kiu/nakabo/nakabo-avr64da32/nakabo-avr64da32-render-B.png

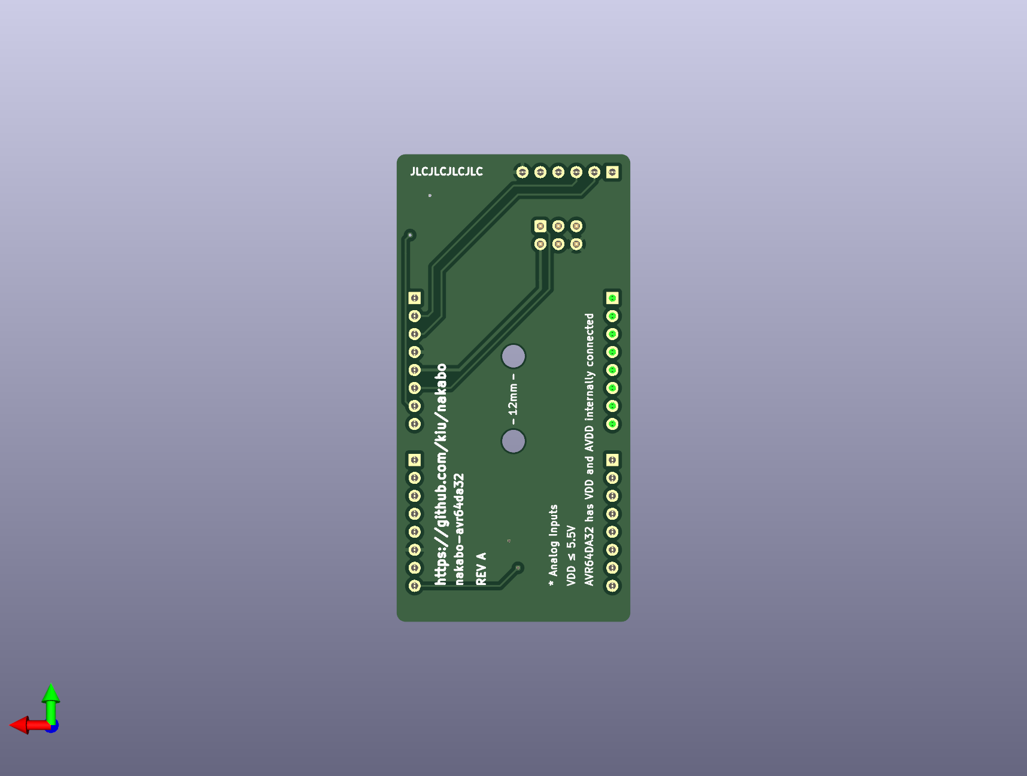
nakabo-avr64da32/nakabo-avr64da32-render-B.png
